CommanderRedYT/ws2812-clock/hardware/leds.kicad_sch

## KiCad design hardware/leds.kicad_sch (2023-09-14)

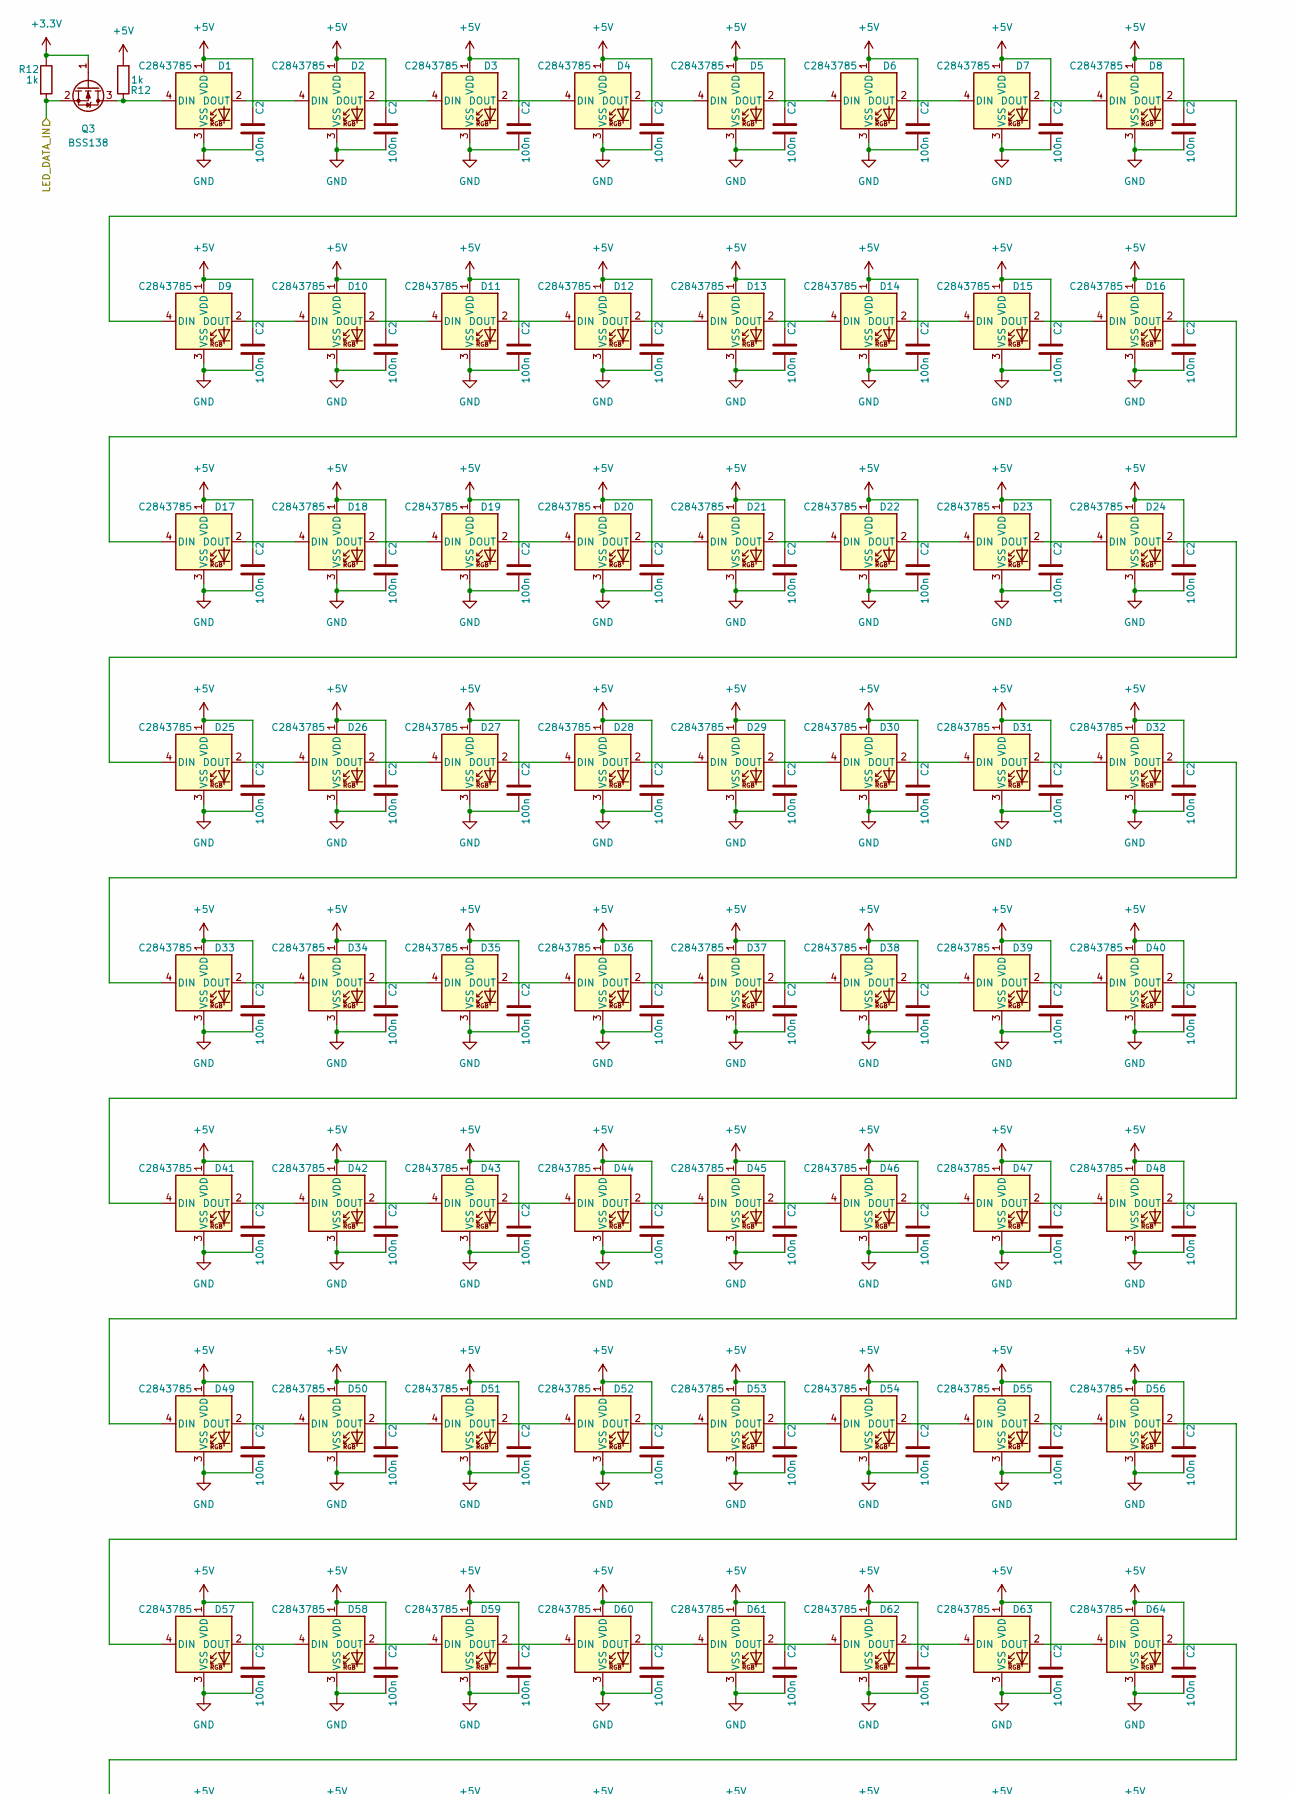
[picture p9: schematic leds.kicad_sch, part in row 1, column 1]

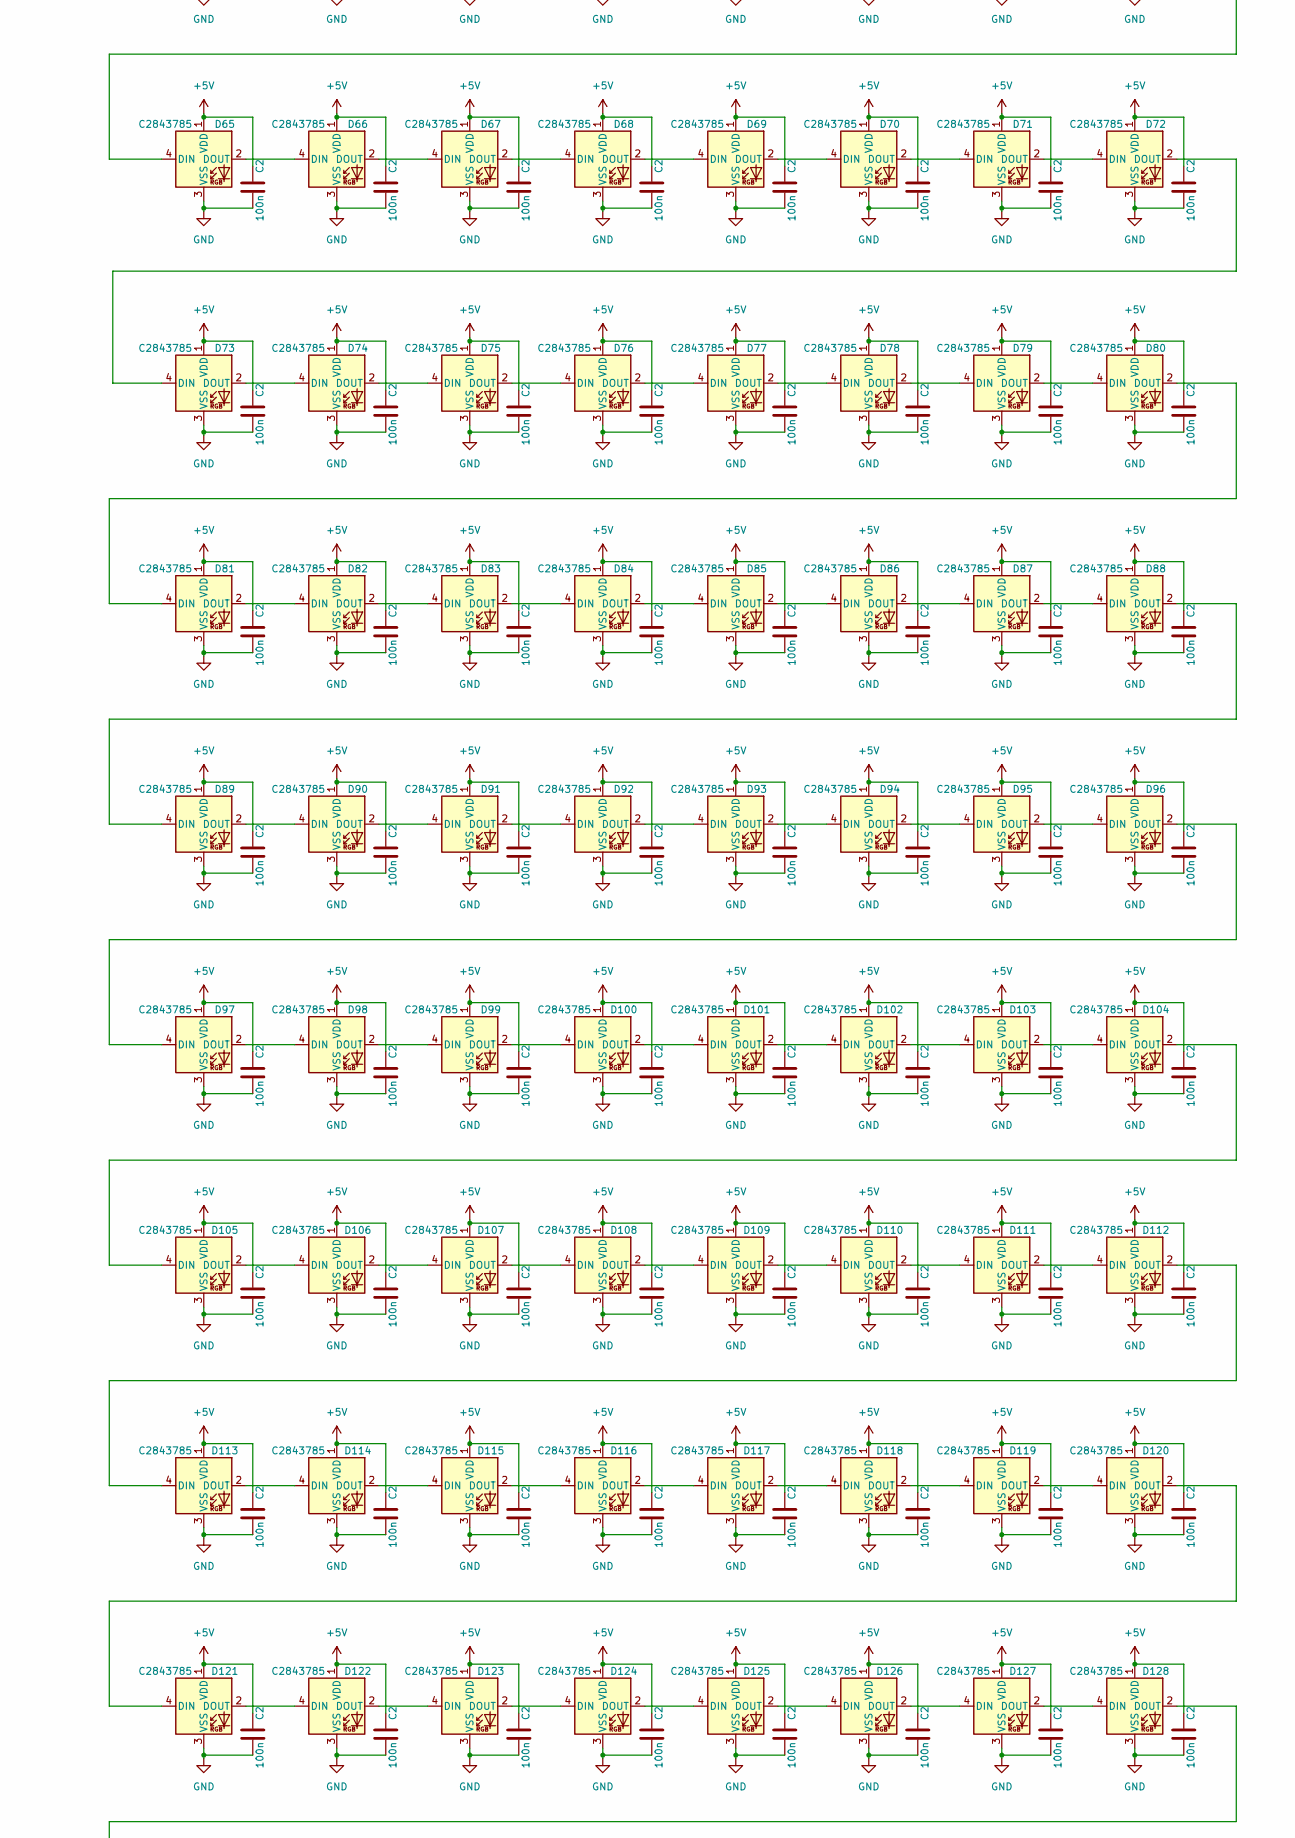
[picture p10: schematic leds.kicad_sch, part in row 2, column 1]

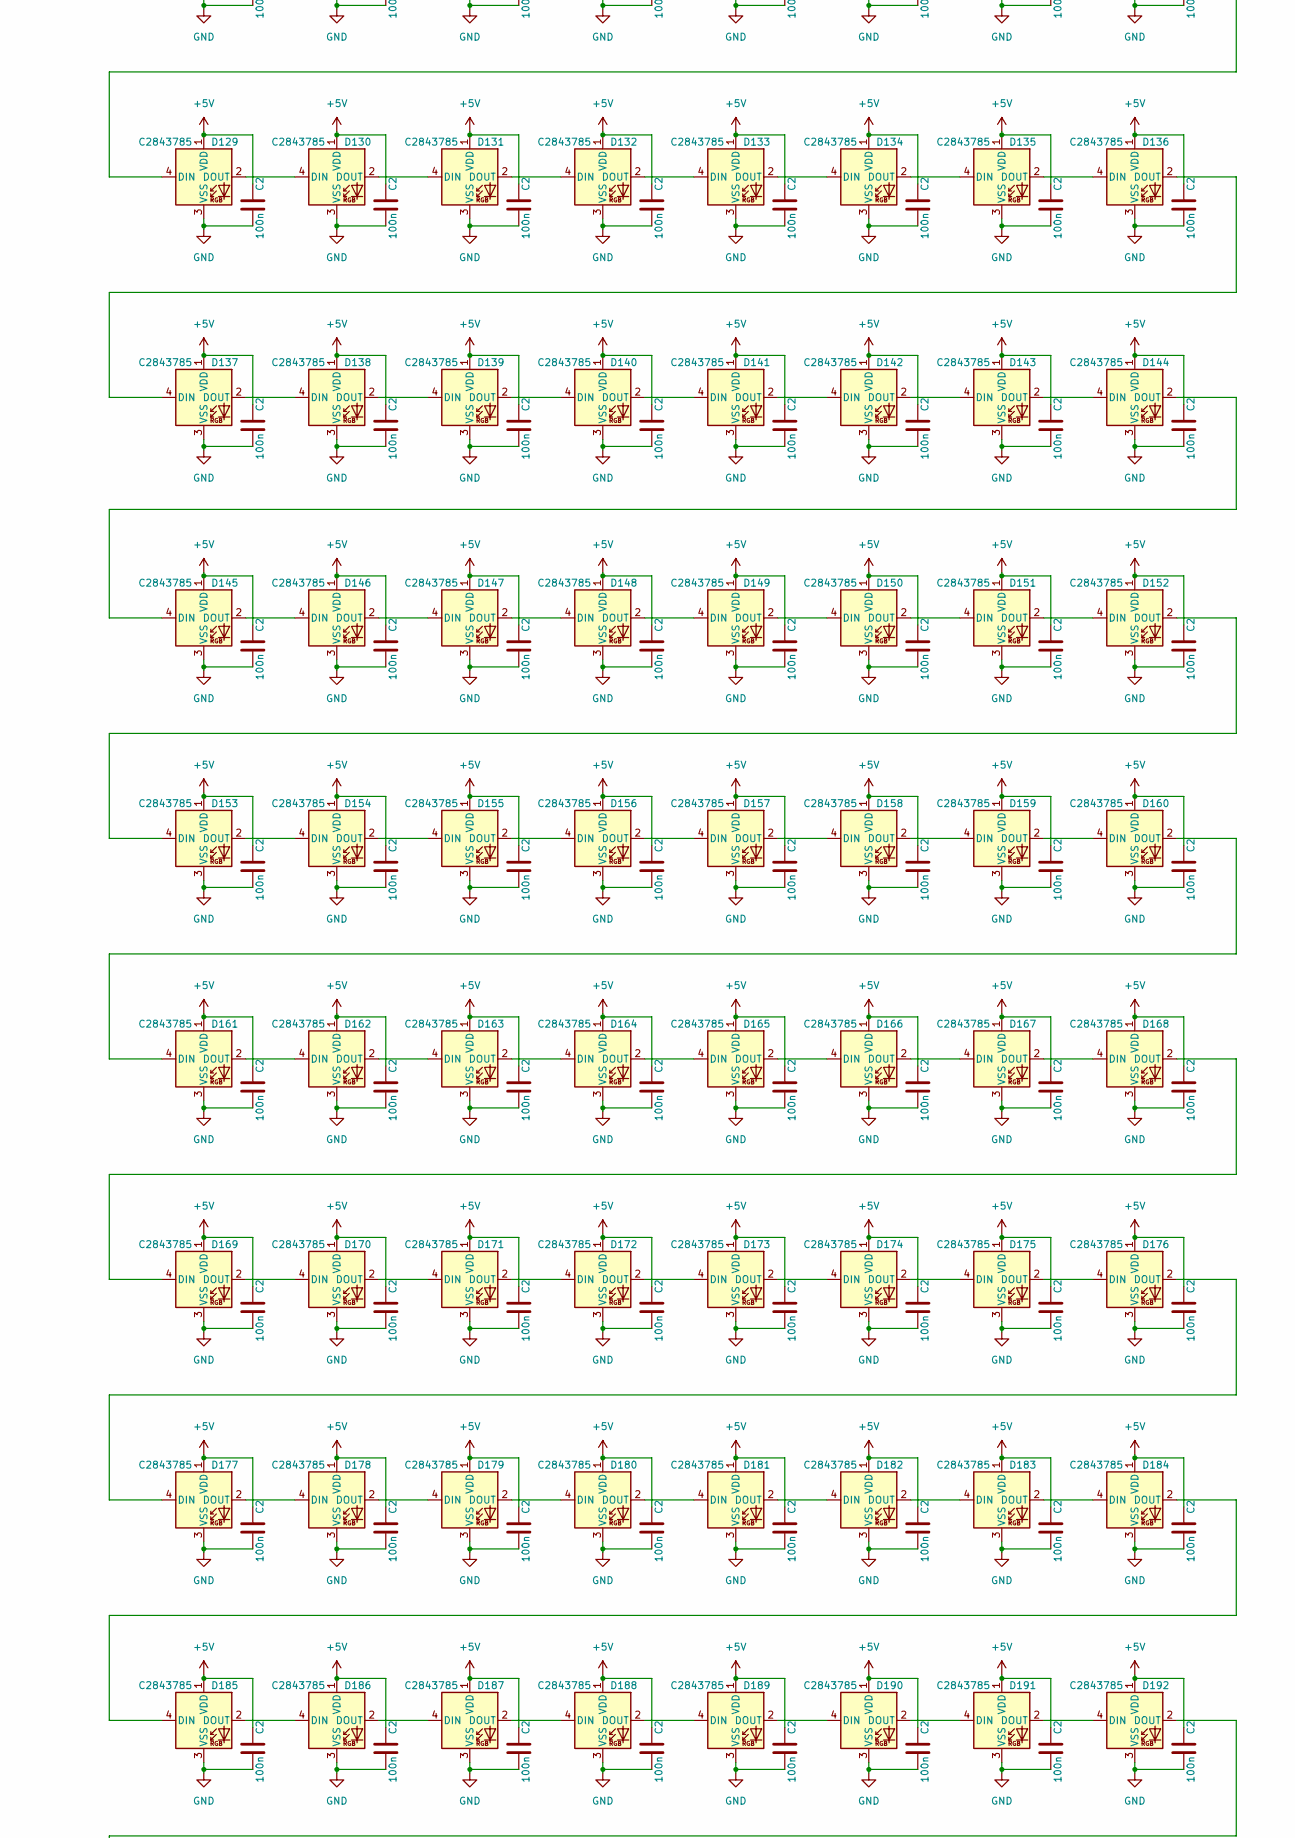
[picture p11: schematic leds.kicad_sch, part in row 3, column 1]

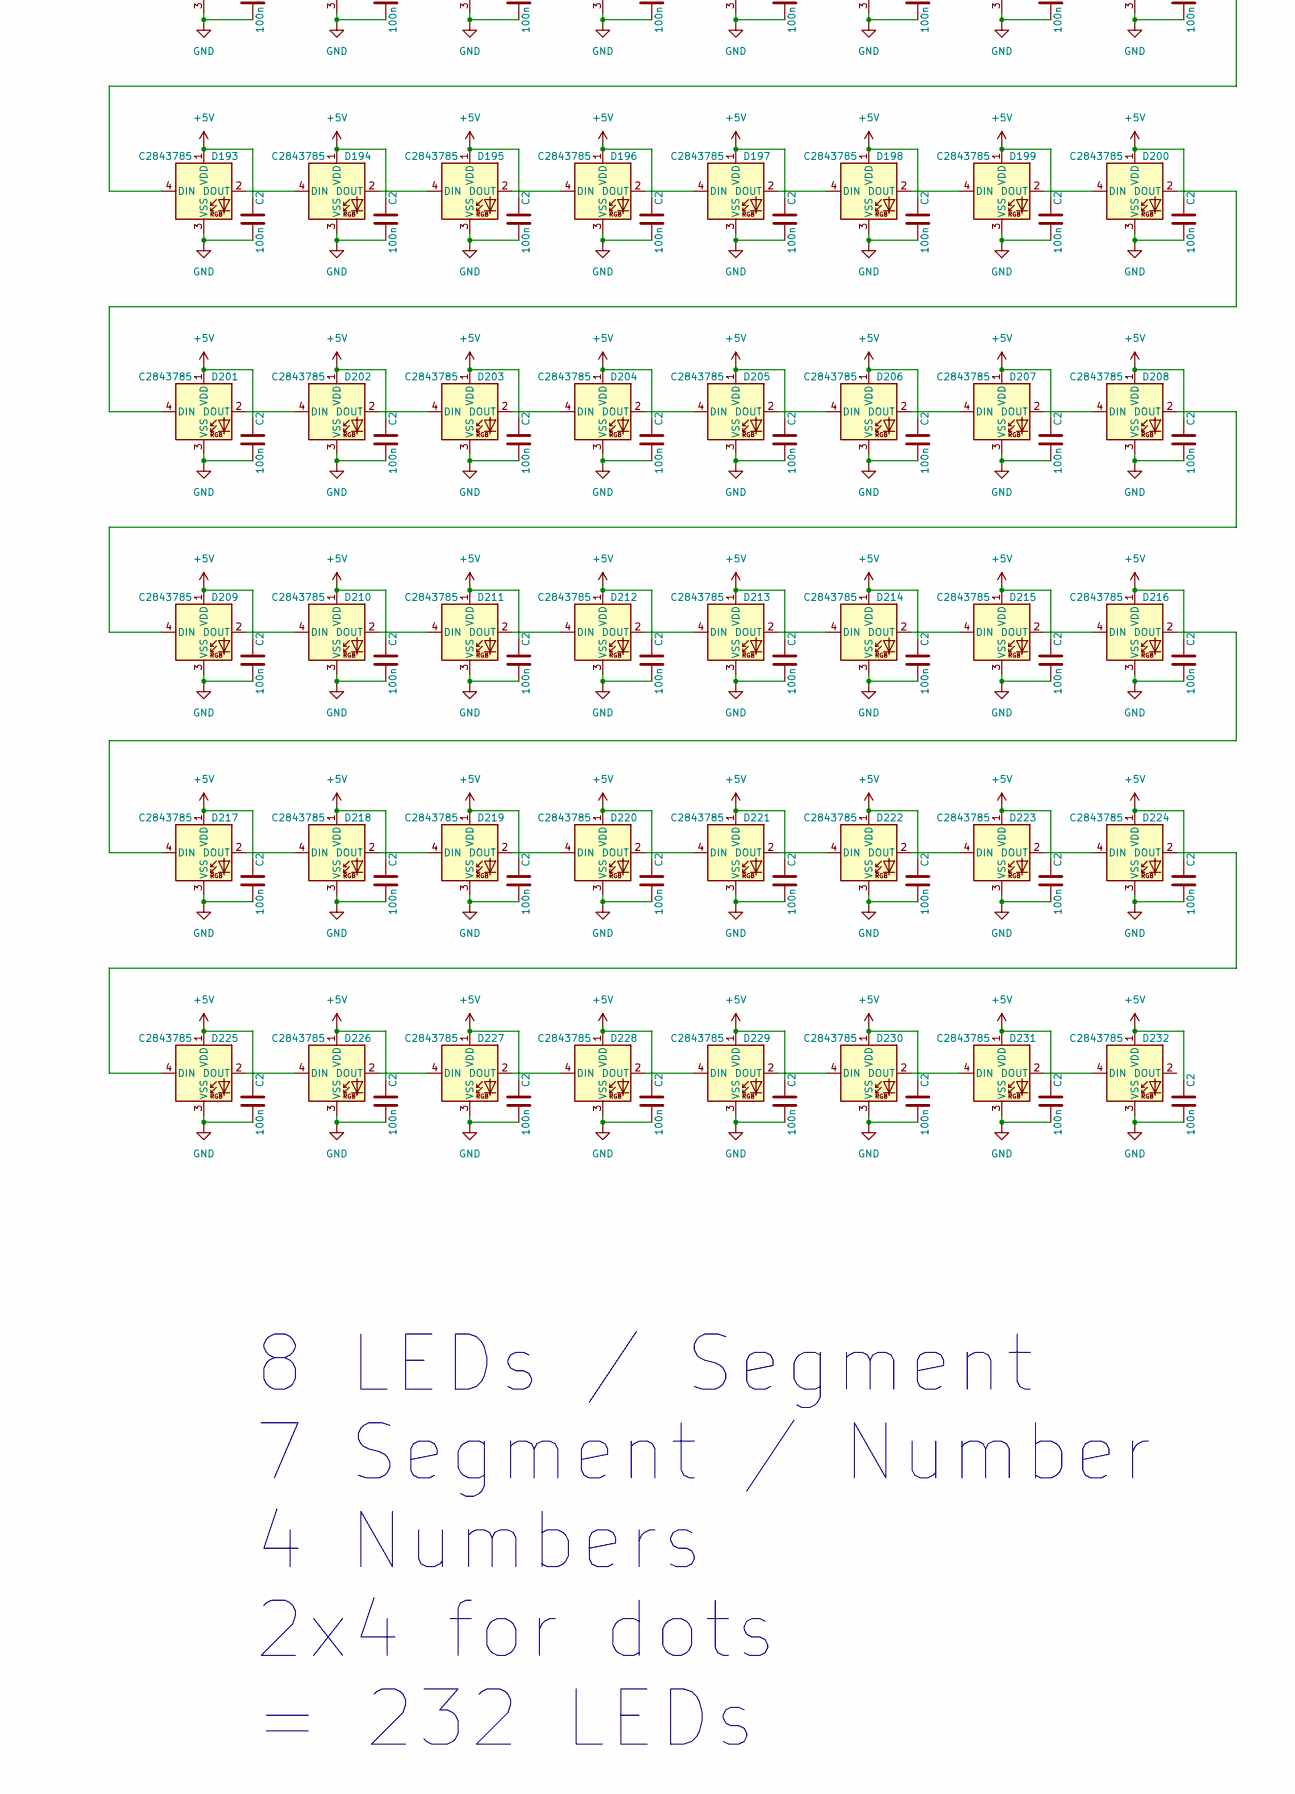
[picture p12: schematic leds.kicad_sch, part in row 4, column 1]

Parts:
C2: 100n; C_0603_1608Metric; LCSC C14663
D1, D2, D3, D4, D5, D6, D7, D8, D9, D10, D11, D12, D13, D14, D15, D16, D17, D18, D19, D20, D21, D22, D23, D24, D25, D26, D27, D28, D29, D30, D31, D32, D33, D34, D35, D36, D37, D38, D39, D40, D41, D42, D43, D44, D45, D46, D47, D48, D49, D50, D51, D52, D53, D54, D55, D56, D57, D58, D59, D60, D61, D62, D63, D64, D65, D66, D67, D68, D69, D70, D71, D72, D73, D74, D75, D76, D77, D78, D79, D80, D81, D82, D83, D84, D85, D86, D87, D88, D89, D90, D91, D92, D93, D94, D95, D96, D97, D98, D99, D100, D101, D102, D103, D104, D105, D106, D107, D108, D109, D110, D111, D112, D113, D114, D115, D116, D117, D118, D119, D120, D121, D122, D123, D124, D125, D126, D127, D128, D129, D130, D131, D132, D133, D134, D135, D136, D137, D138, D139, D140, D141, D142, D143, D144, D145, D146, D147, D148, D149, D150, D151, D152, D153, D154, D155, D156, D157, D158, D159, D160, D161, D162, D163, D164, D165, D166, D167, D168, D169, D170, D171, D172, D173, D174, D175, D176, D177, D178, D179, D180, D181, D182, D183, D184, D185, D186, D187, D188, D189, D190, D191, D192, D193, D194, D195, D196, D197, D198, D199, D200, D201, D202, D203, D204, D205, D206, D207, D208, D209, D210, D211, D212, D213, D214, D215, D216, D217, D218, D219, D220, D221, D222, D223, D224, D225, D226, D227, D228, D229, D230, D231, D232: WS2812B; LED_WS2812B_PLCC4_5.0x5.0mm_P3.2mm; LCSC C2843785
Q3: BSS138; SOT-23; LCSC C112239
R12: 1k; R_0402_1005Metric; LCSC Part # C11702

Connections:
+3.3V: Q3.1 (G), R12.1
+5V: C2.1, D1.1 (VDD), D2.1 (VDD), D3.1 (VDD), D4.1 (VDD), D5.1 (VDD), D6.1 (VDD), D7.1 (VDD), D8.1 (VDD), D9.1 (VDD), D10.1 (VDD), D11.1 (VDD), D12.1 (VDD), D13.1 (VDD), D14.1 (VDD), D15.1 (VDD), D16.1 (VDD), D17.1 (VDD), D18.1 (VDD), D19.1 (VDD), D20.1 (VDD), D21.1 (VDD), D22.1 (VDD), D23.1 (VDD), D24.1 (VDD), D25.1 (VDD), D26.1 (VDD), D27.1 (VDD), D28.1 (VDD), D29.1 (VDD), D30.1 (VDD), D31.1 (VDD), D32.1 (VDD), D33.1 (VDD), D34.1 (VDD), D35.1 (VDD), D36.1 (VDD), D37.1 (VDD), D38.1 (VDD), D39.1 (VDD), D40.1 (VDD), D41.1 (VDD), D42.1 (VDD), D43.1 (VDD), D44.1 (VDD), D45.1 (VDD), D46.1 (VDD), D47.1 (VDD), D48.1 (VDD), D49.1 (VDD), D50.1 (VDD), D51.1 (VDD), D52.1 (VDD), D53.1 (VDD), D54.1 (VDD), D55.1 (VDD), D56.1 (VDD), D57.1 (VDD), D58.1 (VDD), D59.1 (VDD), D60.1 (VDD), D61.1 (VDD), D62.1 (VDD), D63.1 (VDD), D64.1 (VDD), D65.1 (VDD), D66.1 (VDD), D67.1 (VDD), D68.1 (VDD), D69.1 (VDD), D70.1 (VDD), D71.1 (VDD), D72.1 (VDD), D73.1 (VDD), D74.1 (VDD), D75.1 (VDD), D76.1 (VDD), D77.1 (VDD), D78.1 (VDD), D79.1 (VDD), D80.1 (VDD), D81.1 (VDD), D82.1 (VDD), D83.1 (VDD), D84.1 (VDD), D85.1 (VDD), D86.1 (VDD), D87.1 (VDD), D88.1 (VDD), D89.1 (VDD), D90.1 (VDD), D91.1 (VDD), D92.1 (VDD), D93.1 (VDD), D94.1 (VDD), D95.1 (VDD), D96.1 (VDD), D97.1 (VDD), D98.1 (VDD), D99.1 (VDD), D100.1 (VDD), D101.1 (VDD), D102.1 (VDD), D103.1 (VDD), D104.1 (VDD), D105.1 (VDD), D106.1 (VDD), D107.1 (VDD), D108.1 (VDD), D109.1 (VDD), D110.1 (VDD), D111.1 (VDD), D112.1 (VDD), D113.1 (VDD), D114.1 (VDD), D115.1 (VDD), D116.1 (VDD), D117.1 (VDD), D118.1 (VDD), D119.1 (VDD), D120.1 (VDD), D121.1 (VDD), D122.1 (VDD), D123.1 (VDD), D124.1 (VDD), D125.1 (VDD), D126.1 (VDD), D127.1 (VDD), D128.1 (VDD), D129.1 (VDD), D130.1 (VDD), D131.1 (VDD), D132.1 (VDD), D133.1 (VDD), D134.1 (VDD), D135.1 (VDD), D136.1 (VDD), D137.1 (VDD), D138.1 (VDD), D139.1 (VDD), D140.1 (VDD), D141.1 (VDD), D142.1 (VDD), D143.1 (VDD), D144.1 (VDD), D145.1 (VDD), D146.1 (VDD), D147.1 (VDD), D148.1 (VDD), D149.1 (VDD), D150.1 (VDD), D151.1 (VDD), D152.1 (VDD), D153.1 (VDD), D154.1 (VDD), D155.1 (VDD), D156.1 (VDD), D157.1 (VDD), D158.1 (VDD), D159.1 (VDD), D160.1 (VDD), D161.1 (VDD), D162.1 (VDD), D163.1 (VDD), D164.1 (VDD), D165.1 (VDD), D166.1 (VDD), D167.1 (VDD), D168.1 (VDD), D169.1 (VDD), D170.1 (VDD), D171.1 (VDD), D172.1 (VDD), D173.1 (VDD), D174.1 (VDD), D175.1 (VDD), D176.1 (VDD), D177.1 (VDD), D178.1 (VDD), D179.1 (VDD), D180.1 (VDD), D181.1 (VDD), D182.1 (VDD), D183.1 (VDD), D184.1 (VDD), D185.1 (VDD), D186.1 (VDD), D187.1 (VDD), D188.1 (VDD), D189.1 (VDD), D190.1 (VDD), D191.1 (VDD), D192.1 (VDD), D193.1 (VDD), D194.1 (VDD), D195.1 (VDD), D196.1 (VDD), D197.1 (VDD), D198.1 (VDD), D199.1 (VDD), D200.1 (VDD), D201.1 (VDD), D202.1 (VDD), D203.1 (VDD), D204.1 (VDD), D205.1 (VDD), D206.1 (VDD), D207.1 (VDD), D208.1 (VDD), D209.1 (VDD), D210.1 (VDD), D211.1 (VDD), D212.1 (VDD), D213.1 (VDD), D214.1 (VDD), D215.1 (VDD), D216.1 (VDD), D217.1 (VDD), D218.1 (VDD), D219.1 (VDD), D220.1 (VDD), D221.1 (VDD), D222.1 (VDD), D223.1 (VDD), D224.1 (VDD), D225.1 (VDD), D226.1 (VDD), D227.1 (VDD), D228.1 (VDD), D229.1 (VDD), D230.1 (VDD), D231.1 (VDD), D232.1 (VDD), R12.2
GND: C2.2, D1.3 (VSS), D2.3 (VSS), D3.3 (VSS), D4.3 (VSS), D5.3 (VSS), D6.3 (VSS), D7.3 (VSS), D8.3 (VSS), D9.3 (VSS), D10.3 (VSS), D11.3 (VSS), D12.3 (VSS), D13.3 (VSS), D14.3 (VSS), D15.3 (VSS), D16.3 (VSS), D17.3 (VSS), D18.3 (VSS), D19.3 (VSS), D20.3 (VSS), D21.3 (VSS), D22.3 (VSS), D23.3 (VSS), D24.3 (VSS), D25.3 (VSS), D26.3 (VSS), D27.3 (VSS), D28.3 (VSS), D29.3 (VSS), D30.3 (VSS), D31.3 (VSS), D32.3 (VSS), D33.3 (VSS), D34.3 (VSS), D35.3 (VSS), D36.3 (VSS), D37.3 (VSS), D38.3 (VSS), D39.3 (VSS), D40.3 (VSS), D41.3 (VSS), D42.3 (VSS), D43.3 (VSS), D44.3 (VSS), D45.3 (VSS), D46.3 (VSS), D47.3 (VSS), D48.3 (VSS), D49.3 (VSS), D50.3 (VSS), D51.3 (VSS), D52.3 (VSS), D53.3 (VSS), D54.3 (VSS), D55.3 (VSS), D56.3 (VSS), D57.3 (VSS), D58.3 (VSS), D59.3 (VSS), D60.3 (VSS), D61.3 (VSS), D62.3 (VSS), D63.3 (VSS), D64.3 (VSS), D65.3 (VSS), D66.3 (VSS), D67.3 (VSS), D68.3 (VSS), D69.3 (VSS), D70.3 (VSS), D71.3 (VSS), D72.3 (VSS), D73.3 (VSS), D74.3 (VSS), D75.3 (VSS), D76.3 (VSS), D77.3 (VSS), D78.3 (VSS), D79.3 (VSS), D80.3 (VSS), D81.3 (VSS), D82.3 (VSS), D83.3 (VSS), D84.3 (VSS), D85.3 (VSS), D86.3 (VSS), D87.3 (VSS), D88.3 (VSS), D89.3 (VSS), D90.3 (VSS), D91.3 (VSS), D92.3 (VSS), D93.3 (VSS), D94.3 (VSS), D95.3 (VSS), D96.3 (VSS), D97.3 (VSS), D98.3 (VSS), D99.3 (VSS), D100.3 (VSS), D101.3 (VSS), D102.3 (VSS), D103.3 (VSS), D104.3 (VSS), D105.3 (VSS), D106.3 (VSS), D107.3 (VSS), D108.3 (VSS), D109.3 (VSS), D110.3 (VSS), D111.3 (VSS), D112.3 (VSS), D113.3 (VSS), D114.3 (VSS), D115.3 (VSS), D116.3 (VSS), D117.3 (VSS), D118.3 (VSS), D119.3 (VSS), D120.3 (VSS), D121.3 (VSS), D122.3 (VSS), D123.3 (VSS), D124.3 (VSS), D125.3 (VSS), D126.3 (VSS), D127.3 (VSS), D128.3 (VSS), D129.3 (VSS), D130.3 (VSS), D131.3 (VSS), D132.3 (VSS), D133.3 (VSS), D134.3 (VSS), D135.3 (VSS), D136.3 (VSS), D137.3 (VSS), D138.3 (VSS), D139.3 (VSS), D140.3 (VSS), D141.3 (VSS), D142.3 (VSS), D143.3 (VSS), D144.3 (VSS), D145.3 (VSS), D146.3 (VSS), D147.3 (VSS), D148.3 (VSS), D149.3 (VSS), D150.3 (VSS), D151.3 (VSS), D152.3 (VSS), D153.3 (VSS), D154.3 (VSS), D155.3 (VSS), D156.3 (VSS), D157.3 (VSS), D158.3 (VSS), D159.3 (VSS), D160.3 (VSS), D161.3 (VSS), D162.3 (VSS), D163.3 (VSS), D164.3 (VSS), D165.3 (VSS), D166.3 (VSS), D167.3 (VSS), D168.3 (VSS), D169.3 (VSS), D170.3 (VSS), D171.3 (VSS), D172.3 (VSS), D173.3 (VSS), D174.3 (VSS), D175.3 (VSS), D176.3 (VSS), D177.3 (VSS), D178.3 (VSS), D179.3 (VSS), D180.3 (VSS), D181.3 (VSS), D182.3 (VSS), D183.3 (VSS), D184.3 (VSS), D185.3 (VSS), D186.3 (VSS), D187.3 (VSS), D188.3 (VSS), D189.3 (VSS), D190.3 (VSS), D191.3 (VSS), D192.3 (VSS), D193.3 (VSS), D194.3 (VSS), D195.3 (VSS), D196.3 (VSS), D197.3 (VSS), D198.3 (VSS), D199.3 (VSS), D200.3 (VSS), D201.3 (VSS), D202.3 (VSS), D203.3 (VSS), D204.3 (VSS), D205.3 (VSS), D206.3 (VSS), D207.3 (VSS), D208.3 (VSS), D209.3 (VSS), D210.3 (VSS), D211.3 (VSS), D212.3 (VSS), D213.3 (VSS), D214.3 (VSS), D215.3 (VSS), D216.3 (VSS), D217.3 (VSS), D218.3 (VSS), D219.3 (VSS), D220.3 (VSS), D221.3 (VSS), D222.3 (VSS), D223.3 (VSS), D224.3 (VSS), D225.3 (VSS), D226.3 (VSS), D227.3 (VSS), D228.3 (VSS), D229.3 (VSS), D230.3 (VSS), D231.3 (VSS), D232.3 (VSS)
LED_DATA_IN: Q3.2 (S), R12.2
unnamed: D1.2 (DOUT), D2.4 (DIN)
unnamed: D1.4 (DIN), Q3.3 (D), R12.1
unnamed: D2.2 (DOUT), D3.4 (DIN)
unnamed: D3.2 (DOUT), D4.4 (DIN)
unnamed: D4.2 (DOUT), D5.4 (DIN)
unnamed: D5.2 (DOUT), D6.4 (DIN)
unnamed: D6.2 (DOUT), D7.4 (DIN)
unnamed: D7.2 (DOUT), D8.4 (DIN)
unnamed: D8.2 (DOUT), D9.4 (DIN)
unnamed: D10.2 (DOUT), D11.4 (DIN)
unnamed: D9.2 (DOUT), D10.4 (DIN)
unnamed: D11.2 (DOUT), D12.4 (DIN)
unnamed: D12.2 (DOUT), D13.4 (DIN)
unnamed: D13.2 (DOUT), D14.4 (DIN)
unnamed: D14.2 (DOUT), D15.4 (DIN)
unnamed: D15.2 (DOUT), D16.4 (DIN)
unnamed: D16.2 (DOUT), D17.4 (DIN)
unnamed: D17.2 (DOUT), D18.4 (DIN)
unnamed: D18.2 (DOUT), D19.4 (DIN)
unnamed: D19.2 (DOUT), D20.4 (DIN)
unnamed: D20.2 (DOUT), D21.4 (DIN)
unnamed: D21.2 (DOUT), D22.4 (DIN)
unnamed: D22.2 (DOUT), D23.4 (DIN)
unnamed: D23.2 (DOUT), D24.4 (DIN)
unnamed: D24.2 (DOUT), D25.4 (DIN)
unnamed: D25.2 (DOUT), D26.4 (DIN)
unnamed: D26.2 (DOUT), D27.4 (DIN)
unnamed: D27.2 (DOUT), D28.4 (DIN)
unnamed: D28.2 (DOUT), D29.4 (DIN)
unnamed: D29.2 (DOUT), D30.4 (DIN)
unnamed: D30.2 (DOUT), D31.4 (DIN)
unnamed: D31.2 (DOUT), D32.4 (DIN)
unnamed: D32.2 (DOUT), D33.4 (DIN)
unnamed: D33.2 (DOUT), D34.4 (DIN)
unnamed: D34.2 (DOUT), D35.4 (DIN)
unnamed: D35.2 (DOUT), D36.4 (DIN)
unnamed: D36.2 (DOUT), D37.4 (DIN)
unnamed: D37.2 (DOUT), D38.4 (DIN)
unnamed: D38.2 (DOUT), D39.4 (DIN)
unnamed: D39.2 (DOUT), D40.4 (DIN)
unnamed: D40.2 (DOUT), D41.4 (DIN)
unnamed: D41.2 (DOUT), D42.4 (DIN)
unnamed: D42.2 (DOUT), D43.4 (DIN)
unnamed: D43.2 (DOUT), D44.4 (DIN)
unnamed: D44.2 (DOUT), D45.4 (DIN)
unnamed: D45.2 (DOUT), D46.4 (DIN)
unnamed: D46.2 (DOUT), D47.4 (DIN)
unnamed: D47.2 (DOUT), D48.4 (DIN)
unnamed: D48.2 (DOUT), D49.4 (DIN)
unnamed: D49.2 (DOUT), D50.4 (DIN)
unnamed: D50.2 (DOUT), D51.4 (DIN)
unnamed: D51.2 (DOUT), D52.4 (DIN)
unnamed: D52.2 (DOUT), D53.4 (DIN)
unnamed: D53.2 (DOUT), D54.4 (DIN)
unnamed: D54.2 (DOUT), D55.4 (DIN)
unnamed: D55.2 (DOUT), D56.4 (DIN)
unnamed: D56.2 (DOUT), D57.4 (DIN)
unnamed: D57.2 (DOUT), D58.4 (DIN)
unnamed: D58.2 (DOUT), D59.4 (DIN)
unnamed: D59.2 (DOUT), D60.4 (DIN)
unnamed: D60.2 (DOUT), D61.4 (DIN)
unnamed: D61.2 (DOUT), D62.4 (DIN)
unnamed: D62.2 (DOUT), D63.4 (DIN)
unnamed: D63.2 (DOUT), D64.4 (DIN)
unnamed: D64.2 (DOUT), D65.4 (DIN)
unnamed: D65.2 (DOUT), D66.4 (DIN)
unnamed: D66.2 (DOUT), D67.4 (DIN)
unnamed: D67.2 (DOUT), D68.4 (DIN)
unnamed: D68.2 (DOUT), D69.4 (DIN)
unnamed: D69.2 (DOUT), D70.4 (DIN)
unnamed: D70.2 (DOUT), D71.4 (DIN)
unnamed: D71.2 (DOUT), D72.4 (DIN)
unnamed: D72.2 (DOUT), D73.4 (DIN)
unnamed: D73.2 (DOUT), D74.4 (DIN)
unnamed: D74.2 (DOUT), D75.4 (DIN)
unnamed: D75.2 (DOUT), D76.4 (DIN)
unnamed: D76.2 (DOUT), D77.4 (DIN)
unnamed: D77.2 (DOUT), D78.4 (DIN)
unnamed: D78.2 (DOUT), D79.4 (DIN)
unnamed: D79.2 (DOUT), D80.4 (DIN)
unnamed: D80.2 (DOUT), D81.4 (DIN)
unnamed: D81.2 (DOUT), D82.4 (DIN)
unnamed: D82.2 (DOUT), D83.4 (DIN)
unnamed: D83.2 (DOUT), D84.4 (DIN)
unnamed: D84.2 (DOUT), D85.4 (DIN)
unnamed: D85.2 (DOUT), D86.4 (DIN)
unnamed: D86.2 (DOUT), D87.4 (DIN)
unnamed: D87.2 (DOUT), D88.4 (DIN)
unnamed: D88.2 (DOUT), D89.4 (DIN)
unnamed: D89.2 (DOUT), D90.4 (DIN)
unnamed: D90.2 (DOUT), D91.4 (DIN)
unnamed: D91.2 (DOUT), D92.4 (DIN)
unnamed: D92.2 (DOUT), D93.4 (DIN)
unnamed: D93.2 (DOUT), D94.4 (DIN)
unnamed: D94.2 (DOUT), D95.4 (DIN)
unnamed: D95.2 (DOUT), D96.4 (DIN)
unnamed: D96.2 (DOUT), D97.4 (DIN)
unnamed: D97.2 (DOUT), D98.4 (DIN)
unnamed: D98.2 (DOUT), D99.4 (DIN)
unnamed: D100.2 (DOUT), D101.4 (DIN)
unnamed: D99.2 (DOUT), D100.4 (DIN)
unnamed: D101.2 (DOUT), D102.4 (DIN)
unnamed: D102.2 (DOUT), D103.4 (DIN)
unnamed: D103.2 (DOUT), D104.4 (DIN)
unnamed: D104.2 (DOUT), D105.4 (DIN)
unnamed: D105.2 (DOUT), D106.4 (DIN)
unnamed: D106.2 (DOUT), D107.4 (DIN)
unnamed: D107.2 (DOUT), D108.4 (DIN)
unnamed: D108.2 (DOUT), D109.4 (DIN)
unnamed: D109.2 (DOUT), D110.4 (DIN)
unnamed: D110.2 (DOUT), D111.4 (DIN)
unnamed: D111.2 (DOUT), D112.4 (DIN)
unnamed: D112.2 (DOUT), D113.4 (DIN)
unnamed: D113.2 (DOUT), D114.4 (DIN)
unnamed: D114.2 (DOUT), D115.4 (DIN)
unnamed: D115.2 (DOUT), D116.4 (DIN)
unnamed: D116.2 (DOUT), D117.4 (DIN)
unnamed: D117.2 (DOUT), D118.4 (DIN)
unnamed: D118.2 (DOUT), D119.4 (DIN)
unnamed: D119.2 (DOUT), D120.4 (DIN)
unnamed: D120.2 (DOUT), D121.4 (DIN)
unnamed: D121.2 (DOUT), D122.4 (DIN)
unnamed: D122.2 (DOUT), D123.4 (DIN)
unnamed: D123.2 (DOUT), D124.4 (DIN)
unnamed: D124.2 (DOUT), D125.4 (DIN)
unnamed: D125.2 (DOUT), D126.4 (DIN)
unnamed: D126.2 (DOUT), D127.4 (DIN)
unnamed: D127.2 (DOUT), D128.4 (DIN)
unnamed: D128.2 (DOUT), D129.4 (DIN)
unnamed: D129.2 (DOUT), D130.4 (DIN)
unnamed: D130.2 (DOUT), D131.4 (DIN)
unnamed: D131.2 (DOUT), D132.4 (DIN)
unnamed: D132.2 (DOUT), D133.4 (DIN)
unnamed: D133.2 (DOUT), D134.4 (DIN)
unnamed: D134.2 (DOUT), D135.4 (DIN)
unnamed: D135.2 (DOUT), D136.4 (DIN)
unnamed: D136.2 (DOUT), D137.4 (DIN)
unnamed: D137.2 (DOUT), D138.4 (DIN)
unnamed: D138.2 (DOUT), D139.4 (DIN)
unnamed: D139.2 (DOUT), D140.4 (DIN)
unnamed: D140.2 (DOUT), D141.4 (DIN)
unnamed: D141.2 (DOUT), D142.4 (DIN)
unnamed: D142.2 (DOUT), D143.4 (DIN)
unnamed: D143.2 (DOUT), D144.4 (DIN)
unnamed: D144.2 (DOUT), D145.4 (DIN)
unnamed: D145.2 (DOUT), D146.4 (DIN)
unnamed: D146.2 (DOUT), D147.4 (DIN)
unnamed: D147.2 (DOUT), D148.4 (DIN)
unnamed: D148.2 (DOUT), D149.4 (DIN)
unnamed: D149.2 (DOUT), D150.4 (DIN)
unnamed: D150.2 (DOUT), D151.4 (DIN)
unnamed: D151.2 (DOUT), D152.4 (DIN)
unnamed: D152.2 (DOUT), D153.4 (DIN)
unnamed: D153.2 (DOUT), D154.4 (DIN)
unnamed: D154.2 (DOUT), D155.4 (DIN)
unnamed: D155.2 (DOUT), D156.4 (DIN)
unnamed: D156.2 (DOUT), D157.4 (DIN)
unnamed: D157.2 (DOUT), D158.4 (DIN)
unnamed: D158.2 (DOUT), D159.4 (DIN)
unnamed: D159.2 (DOUT), D160.4 (DIN)
unnamed: D160.2 (DOUT), D161.4 (DIN)
unnamed: D161.2 (DOUT), D162.4 (DIN)
unnamed: D162.2 (DOUT), D163.4 (DIN)
unnamed: D163.2 (DOUT), D164.4 (DIN)
unnamed: D164.2 (DOUT), D165.4 (DIN)
unnamed: D165.2 (DOUT), D166.4 (DIN)
unnamed: D166.2 (DOUT), D167.4 (DIN)
unnamed: D167.2 (DOUT), D168.4 (DIN)
unnamed: D168.2 (DOUT), D169.4 (DIN)
unnamed: D169.2 (DOUT), D170.4 (DIN)
unnamed: D170.2 (DOUT), D171.4 (DIN)
unnamed: D171.2 (DOUT), D172.4 (DIN)
unnamed: D172.2 (DOUT), D173.4 (DIN)
unnamed: D173.2 (DOUT), D174.4 (DIN)
unnamed: D174.2 (DOUT), D175.4 (DIN)
unnamed: D175.2 (DOUT), D176.4 (DIN)
unnamed: D176.2 (DOUT), D177.4 (DIN)
unnamed: D177.2 (DOUT), D178.4 (DIN)
unnamed: D178.2 (DOUT), D179.4 (DIN)
unnamed: D179.2 (DOUT), D180.4 (DIN)
unnamed: D180.2 (DOUT), D181.4 (DIN)
unnamed: D181.2 (DOUT), D182.4 (DIN)
unnamed: D182.2 (DOUT), D183.4 (DIN)
unnamed: D183.2 (DOUT), D184.4 (DIN)
unnamed: D184.2 (DOUT), D185.4 (DIN)
unnamed: D185.2 (DOUT), D186.4 (DIN)
unnamed: D186.2 (DOUT), D187.4 (DIN)
unnamed: D187.2 (DOUT), D188.4 (DIN)
unnamed: D188.2 (DOUT), D189.4 (DIN)
unnamed: D189.2 (DOUT), D190.4 (DIN)
unnamed: D190.2 (DOUT), D191.4 (DIN)
unnamed: D191.2 (DOUT), D192.4 (DIN)
unnamed: D192.2 (DOUT), D193.4 (DIN)
unnamed: D193.2 (DOUT), D194.4 (DIN)
unnamed: D194.2 (DOUT), D195.4 (DIN)
unnamed: D195.2 (DOUT), D196.4 (DIN)
unnamed: D196.2 (DOUT), D197.4 (DIN)
unnamed: D197.2 (DOUT), D198.4 (DIN)
unnamed: D198.2 (DOUT), D199.4 (DIN)
unnamed: D199.2 (DOUT), D200.4 (DIN)
unnamed: D200.2 (DOUT), D201.4 (DIN)
unnamed: D201.2 (DOUT), D202.4 (DIN)
unnamed: D202.2 (DOUT), D203.4 (DIN)
unnamed: D203.2 (DOUT), D204.4 (DIN)
unnamed: D204.2 (DOUT), D205.4 (DIN)
unnamed: D205.2 (DOUT), D206.4 (DIN)
unnamed: D206.2 (DOUT), D207.4 (DIN)
unnamed: D207.2 (DOUT), D208.4 (DIN)
unnamed: D208.2 (DOUT), D209.4 (DIN)
unnamed: D209.2 (DOUT), D210.4 (DIN)
unnamed: D210.2 (DOUT), D211.4 (DIN)
unnamed: D211.2 (DOUT), D212.4 (DIN)
unnamed: D212.2 (DOUT), D213.4 (DIN)
unnamed: D213.2 (DOUT), D214.4 (DIN)
unnamed: D214.2 (DOUT), D215.4 (DIN)
unnamed: D215.2 (DOUT), D216.4 (DIN)
unnamed: D216.2 (DOUT), D217.4 (DIN)
unnamed: D217.2 (DOUT), D218.4 (DIN)
unnamed: D218.2 (DOUT), D219.4 (DIN)
unnamed: D219.2 (DOUT), D220.4 (DIN)
unnamed: D220.2 (DOUT), D221.4 (DIN)
unnamed: D221.2 (DOUT), D222.4 (DIN)
unnamed: D222.2 (DOUT), D223.4 (DIN)
unnamed: D223.2 (DOUT), D224.4 (DIN)
unnamed: D224.2 (DOUT), D225.4 (DIN)
unnamed: D225.2 (DOUT), D226.4 (DIN)
unnamed: D226.2 (DOUT), D227.4 (DIN)
unnamed: D227.2 (DOUT), D228.4 (DIN)
unnamed: D228.2 (DOUT), D229.4 (DIN)
unnamed: D229.2 (DOUT), D230.4 (DIN)
unnamed: D230.2 (DOUT), D231.4 (DIN)
unnamed: D231.2 (DOUT), D232.4 (DIN)

Notes on the sheet:
8 LEDs / Segment 7 Segment / Number 4 Numbers 2x4 for dots = 232 LEDs
