CommanderRedYT/ws2812-clock/hardware/usb_c.kicad_sch

## KiCad design hardware/usb_c.kicad_sch (2023-12-17)

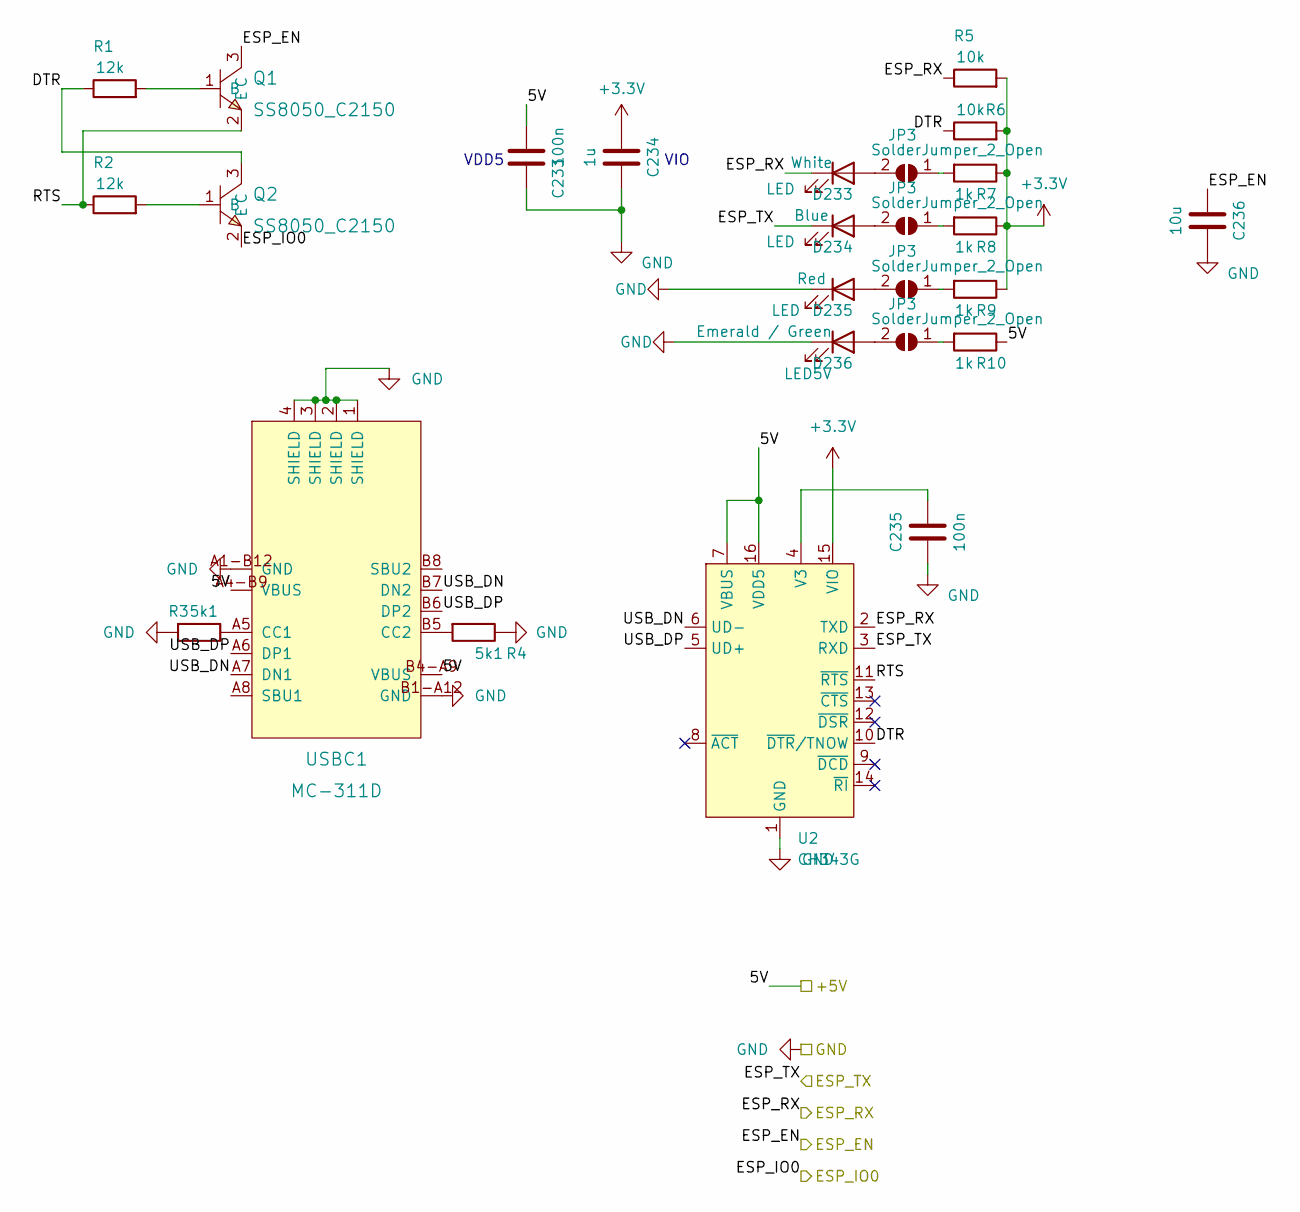
[picture p13: schematic usb_c.kicad_sch]

Parts:
C233, C235: 100n; C_0402_1005Metric; LCSC Part # C1525
C234: 1u; C_0603_1608Metric; LCSC Part # C15849
C236: 10u; C_0603_1608Metric; LCSC Part # C96446
D233: LED; LED_0603_1608Metric; LCSC Part # C2290
D234: LED; LED_0603_1608Metric; LCSC Part # C72041
D235: LED; LED_0603_1608Metric; LCSC Part # C2286
D236: LED5V; LED_0603_1608Metric; LCSC Part # C72043
JP3: SolderJumper_2_Open; SolderJumper-2_P1.3mm_Open_TrianglePad1.0x1.5mm
Q1, Q2: SS8050_C2150; TSOT-23; JLC Part Basic Part
R1, R2: 12k; R_0402_1005Metric; LCSC Part # C25752
R3, R4: 5k1; R_0402_1005Metric; LCSC Part # C25905
R5, R6: 10k; R_0402_1005Metric; LCSC Part # C25744
R7, R8, R9, R10: 1k; R_0402_1005Metric; LCSC Part # C11702
U2: CH343G; SOIC-16_3.9x9.9mm_P1.27mm; LCSC Part # C2844153
USBC1: MC-311D; USB-C-SMD_MC-311D; JLC Part Extended Part

Connections:
+3.3V: C234.2, R5.2, R6.2, R7.1, R8.1, R9.1, U2.15 (VIO)
+5V: C233.2, R10.1, U2.7 (VBUS), U2.16 (VDD5), USBC1.A4-B9 (VBUS), USBC1.B4-A9 (VBUS)
DTR: Q2.3 (C), R1.1, R6.1, U2.10 (~DTR/TNOW)
ESP_EN: C236.2, Q1.3 (C)
ESP_IO0: Q2.2 (E)
ESP_RX: D233.1 (K), R5.1, U2.2 (TXD)
ESP_TX: D234.1 (K), U2.3 (RXD)
GND: C233.1, C234.1, C235.1, C236.1, D235.1 (K), D236.1 (K), R3.2, R4.1, U2.1 (GND), USBC1.1 (SHIELD), USBC1.2 (SHIELD), USBC1.3 (SHIELD), USBC1.4 (SHIELD), USBC1.A1-B12 (GND), USBC1.B1-A12 (GND)
unnamed: C235.2, U2.4 (V3)
unnamed: D233.2 (A), JP3.2 (B)
unnamed: D234.2 (A), JP3.2 (B)
unnamed: D235.2 (A), JP3.2 (B)
unnamed: D236.2 (A), JP3.2 (B)
unnamed: JP3.1 (A), R7.2, R8.2, R9.2, R10.2
unnamed: Q1.1 (B), R1.2
unnamed: Q2.1 (B), R2.2
unnamed: R3.1, USBC1.A5 (CC1)
unnamed: R4.2, USBC1.B5 (CC2)
RTS: Q1.2 (E), R2.1, U2.11 (~RTS)
USB_DN: U2.6 (UD-), USBC1.A7 (DN1), USBC1.B7 (DN2)
USB_DP: U2.5 (UD+), USBC1.A6 (DP1), USBC1.B6 (DP2)

Notes on the sheet:
VDD5
VIO
