CommanderRedYT/ws2812-clock/hardware/ws2812-clock.kicad_sch

## KiCad design hardware/ws2812-clock.kicad_sch (2023-12-17)

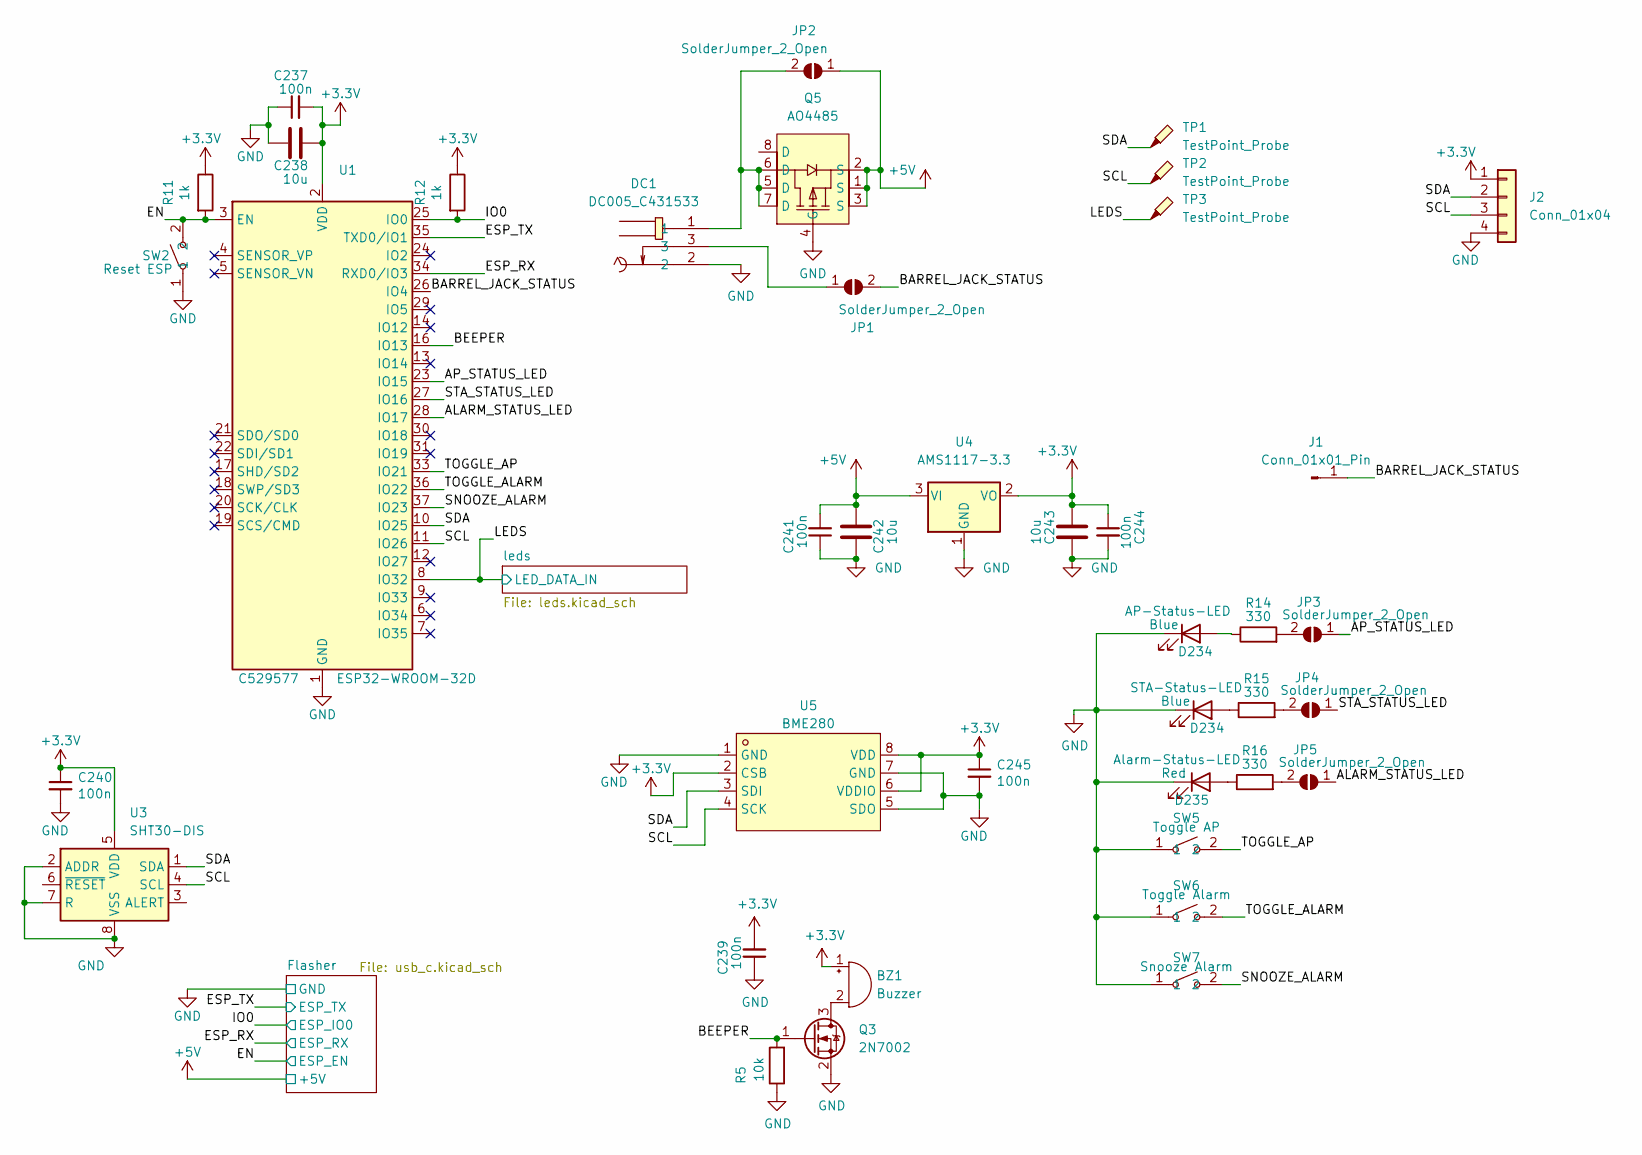
[picture p14: schematic ws2812-clock.kicad_sch]

Parts:
BZ1: Buzzer; LCSC Part # C95299
C237, C239, C240, C241, C244, C245: 100n; C_0402_1005Metric; LCSC Part # C1525
C238, C242, C243: 10u; C_0603_1608Metric; LCSC Part # C19702
D234: STA-Status-LED; LED_0603_1608Metric; LCSC Part # C72041
D235: Alarm-Status-LED; LED_0603_1608Metric; LCSC Part # C2286
DC1: DC005_C431533; DC-IN-TH_DC005; LCSC Part C431533
J1: Conn_01x01_Pin; Pin_D1.0mm_L10.0mm; LCSC DNP
J2: Conn_01x04; PinHeader_1x04_P2.54mm_Vertical
JP1, JP2, JP3, JP4, JP5: SolderJumper_2_Open; SolderJumper-2_P1.3mm_Open_TrianglePad1.0x1.5mm
Q3: 2N7002; SOT-23; LCSC Part # C8545
Q5: AO4485; SOIC-8_L5.0-W4.0-P1.27-LS6.0-BL; LCSC Part C51499
R5: 10k; R_0402_1005Metric; LCSC Part # C25744
R11, R12: 1k; R_0402_1005Metric; LCSC Part # C11702
R14, R15, R16: 330; R_0402_1005Metric; LCSC C25104
SW2: Reset ESP; SW-SMD_L3.9-W3.0-P4.45; LCSC Part C455280
SW5: Toggle AP; SW-SMD_L3.9-W3.0-P4.45; LCSC Part C455280
SW6: Toggle Alarm; SW-SMD_L3.9-W3.0-P4.45; LCSC Part C455280
SW7: Snooze Alarm; SW-SMD_L3.9-W3.0-P4.45; LCSC Part C455280
TP1, TP2, TP3: TestPoint_Probe; TestPoint_Pad_D2.0mm
U1: ESP32-WROOM-32D; LCSC C529577
U3: SHT30-DIS; Sensirion_DFN-8-1EP_2.5x2.5mm_P0.5mm_EP1.1x1.7mm; LCSC Part # C77361
U4: AMS1117-3.3; SOT-223-3_TabPin2; LCSC C6186
U5: BME280; LGA-8_BME280_BL; LCSC Part C92489

Connections:
+3.3V: BZ1.1 (-), C237.2, C238.2, C239.2, C240.1, C243.1, C244.1, C245.1, J2.1, R11.1, R12.1, U1.2 (VDD), U3.5 (VDD), U4.2 (VO), U5.2 (CSB), U5.6 (VDDIO), U5.8 (VDD)
+5V: C241.2, C242.2, JP2.1 (A), Q5.1 (S), Q5.2 (S), Q5.3 (S), U4.3 (VI)
ALARM_STATUS_LED: JP5.1 (A), U1.28 (IO17)
AP_STATUS_LED: JP3.1 (A), U1.23 (IO15)
BARREL_JACK_STATUS: J1.1, JP1.2 (B), U1.26 (IO4)
BEEPER: Q3.1 (G), R5.2, U1.16 (IO13)
EN: R11.2, SW2.2, U1.3 (EN)
ESP_RX: U1.34 (RXD0/IO3)
ESP_TX: U1.35 (TXD0/IO1)
GND: C237.1, C238.1, C239.1, C240.2, C241.1, C242.1, C243.2, C244.2, C245.2, D234.1 (K), D235.1 (K), DC1.2, J2.4, Q3.2 (S), Q5.4 (G), R5.1, SW2.1, SW5.1, SW6.1, SW7.1, U1.1 (GND), U1.15 (GND), U1.38 (GND), U1.39 (GND), U3.2 (ADDR), U3.7 (R), U3.8 (VSS), U3.9 (VSS), U4.1 (GND), U5.1 (GND), U5.5 (SDO), U5.7 (GND)
IO0: R12.2, U1.25 (IO0)
LEDS: TP3.1, U1.8 (IO32)
unnamed: BZ1.2 (+), Q3.3 (D)
unnamed: D234.2 (A), R14.1, R15.1
unnamed: D235.2 (A), R16.1
unnamed: DC1.1, JP2.2 (B), Q5.5 (D), Q5.6 (D), Q5.7 (D)
unnamed: DC1.3, JP1.1 (A)
unnamed: JP3.2 (B), R14.2
unnamed: JP4.2 (B), R15.2
unnamed: JP5.2 (B), R16.2
SCL: J2.3, TP2.1, U1.11 (IO26), U3.4 (SCL), U5.4 (SCK)
SDA: J2.2, TP1.1, U1.10 (IO25), U3.1 (SDA), U5.3 (SDI)
SNOOZE_ALARM: SW7.2, U1.37 (IO23)
STA_STATUS_LED: JP4.1 (A), U1.27 (IO16)
TOGGLE_ALARM: SW6.2, U1.36 (IO22)
TOGGLE_AP: SW5.2, U1.33 (IO21)
