CommanderRedYT/ws2812-clock/firmware/main/peripheral/ledmanager.h

#pragma once

// system includes
#include <array>
#include <string>
#include <utility>

// 3rdparty lib includes
#include <cpptypesafeenum.h>
#include <delayedconstruction.h>
#include <espchrono.h>
#include <wrappers/recursive_mutex_semaphore.h>

// local includes
#include "ledhelpers/digit.h"
#include "ledhelpers/clockdot.h"

#define SecondaryBrightnessModeValues(x) \
    x(Off) \
    x(UseRange) \
    x(UseSunriseSunset)
DECLARE_GLOBAL_TYPESAFE_ENUM(SecondaryBrightnessMode, : uint8_t, SecondaryBrightnessModeValues);

namespace ledmanager {

using LedArray = std::array<CRGB, HARDWARE_WS2812B_COUNT>;

class LedManager
{
    using Digits = std::array<SevenSegmentDigit, 4>;

public:
    LedManager(Digits digits, const ClockDot &upper, const ClockDot &lower)
        : digits{std::move(digits)}, upper_dot{upper}, lower_dot{lower}
    {}

    Digits digits;
    ClockDot upper_dot;
    ClockDot lower_dot;

    void render();

    void setVisible(const bool visible) { m_visible = visible; }

    void handleVoltageAndCurrent();

    static uint16_t getFps();

    float getBrightness() const { return m_brightness; }

    bool isVisible() const { return m_visible && m_brightness > 0; }

    bool setText(std::string_view text);

private:

    std::string toString() const;

    bool m_visible{};

    bool m_dotsOn{};
    bool m_lastDotsOn{};

    float m_brightness{0};
    espchrono::millis_clock::time_point m_brightnessLastUpdate{};

    std::optional<espchrono::millis_clock::time_point> m_overrideTriggeredAt{};
};

extern cpputils::DelayedConstruction<LedManager> ledManager;

extern cpputils::DelayedConstruction<espcpputils::recursive_mutex_semaphore> led_lock;

void begin();

void update();

const LedArray& getLeds();

} // namespace ledmanager
